Blargedy/Pastamatic-Filament-Spool-Winder-Modifications/STLs/1x_driven_target_cradle_clamp_tab.stl

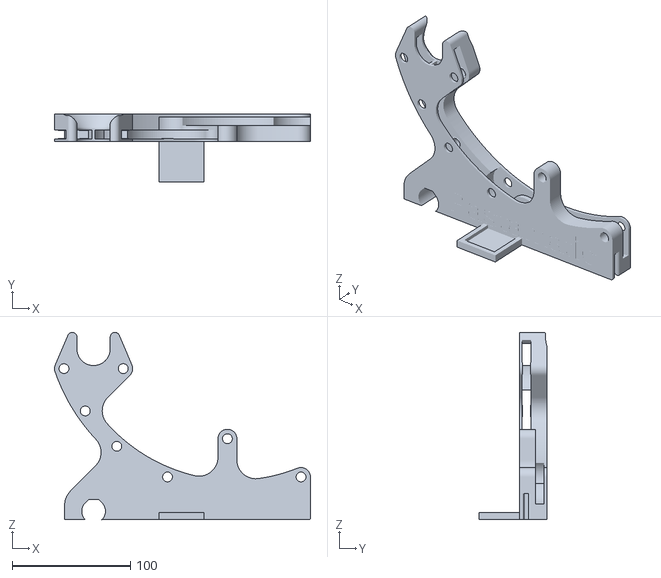
[picture p15: CAD file, 2023-08-05]
STLs/1x_driven_target_cradle_clamp_tab.stl
216.1 x 57.2 x 158.0
