Blargedy/Pastamatic-Filament-Spool-Winder-Modifications/STLs/Options/spindle_spacer_L.stl

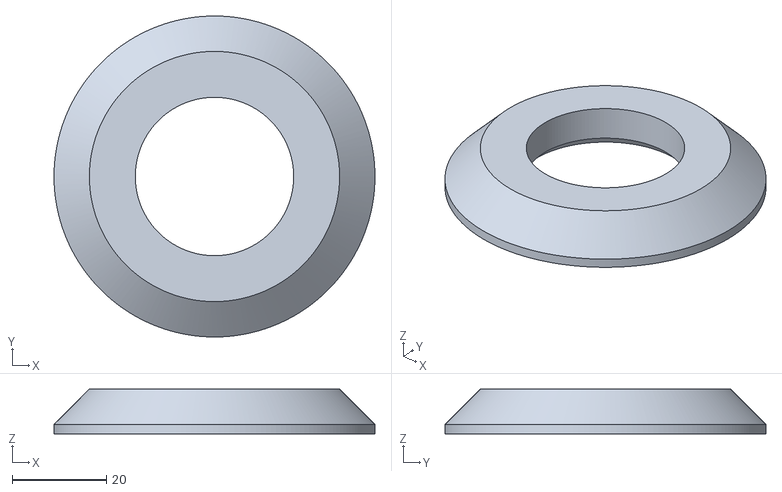
[picture p16: CAD file, 2024-02-23]
STLs/Options/spindle_spacer_L.stl
68.0 x 68.0 x 9.50
