Blargedy/Pastamatic-Filament-Spool-Winder-Modifications/STLs/Options/spacer_storage_cap.stl

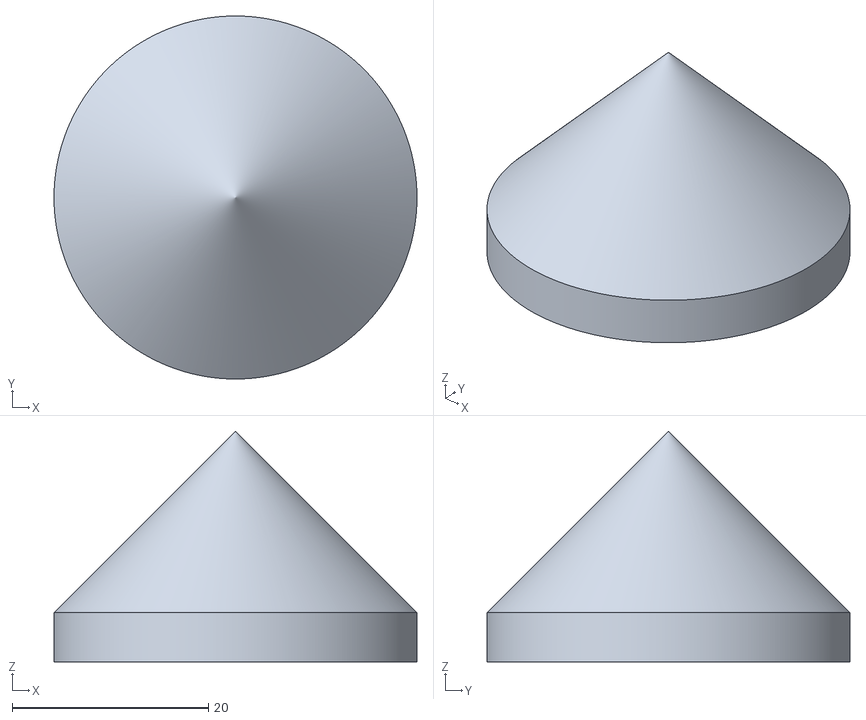
[picture p17: CAD file, 2024-02-23]
STLs/Options/spacer_storage_cap.stl
37.0 x 37.0 x 23.5
