Blargedy/Pastamatic-Filament-Spool-Winder-Modifications/STLs/1x_leadscrew_block_lowered.stl

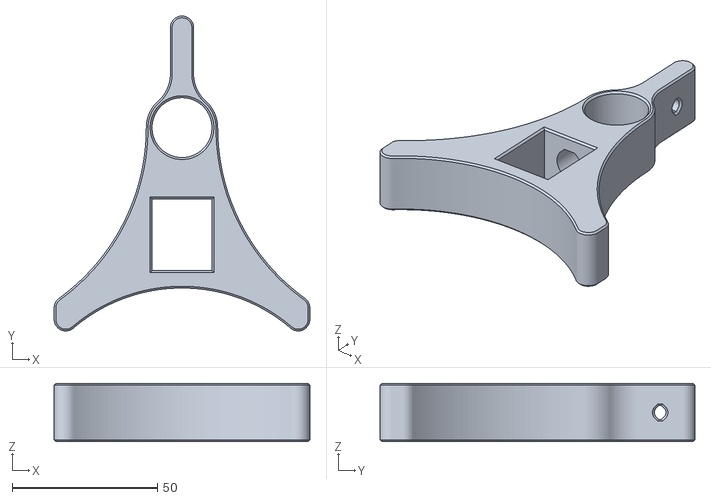
[picture p18: CAD file, 2023-08-05]
STLs/1x_leadscrew_block_lowered.stl
88.0 x 108.4 x 20.0
